hornej/open-task-light/DIYson Express/Printed Parts/STL/Charging Base (optional).stl

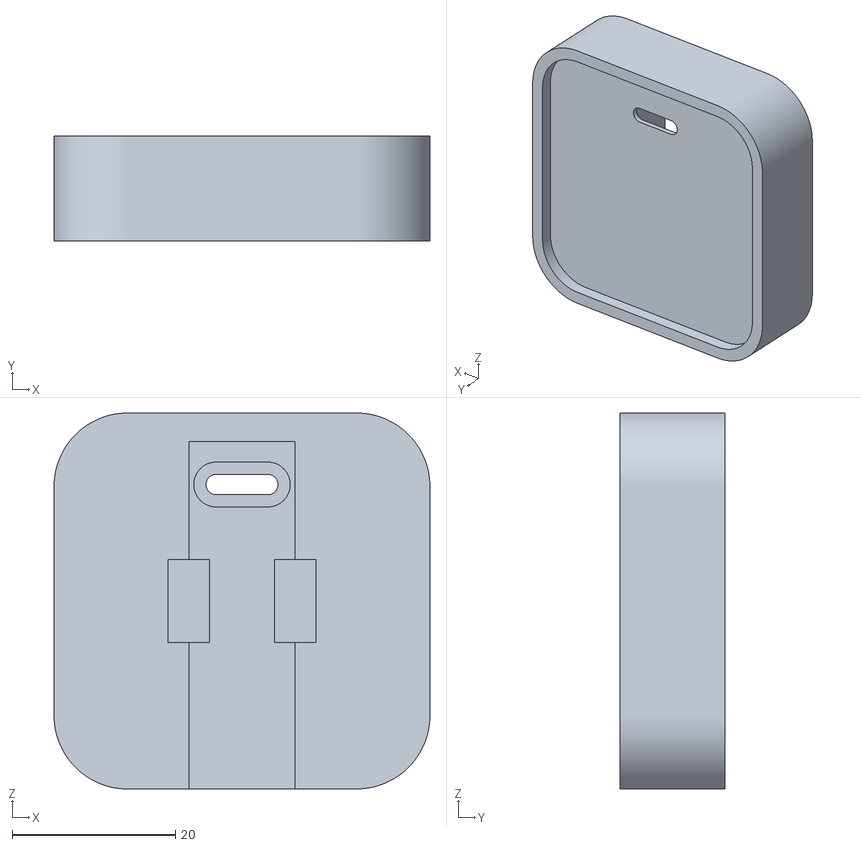
[picture p15: CAD file, 2023-01-30, last stored version]
DIYson Express/Printed Parts/STL/Charging Base (optional).stl
46.0 x 12.8 x 46.0
