hornej/open-task-light/DIYson/Mechanical/STEP/LED Cover - Top.step

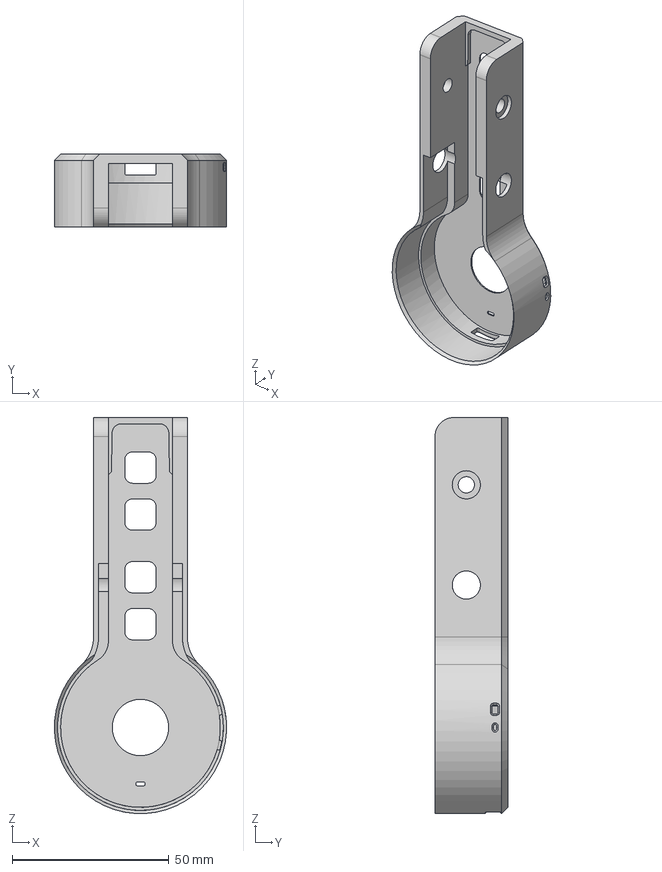
[picture p16: CAD file, 2025-01-30, last stored version]
DIYson/Mechanical/STEP/LED Cover - Top.step
55.0 x 23.3 x 126.5 mm
