hornej/open-task-light/DIYson/Mechanical/STL/Decrease Brightness Button.stl

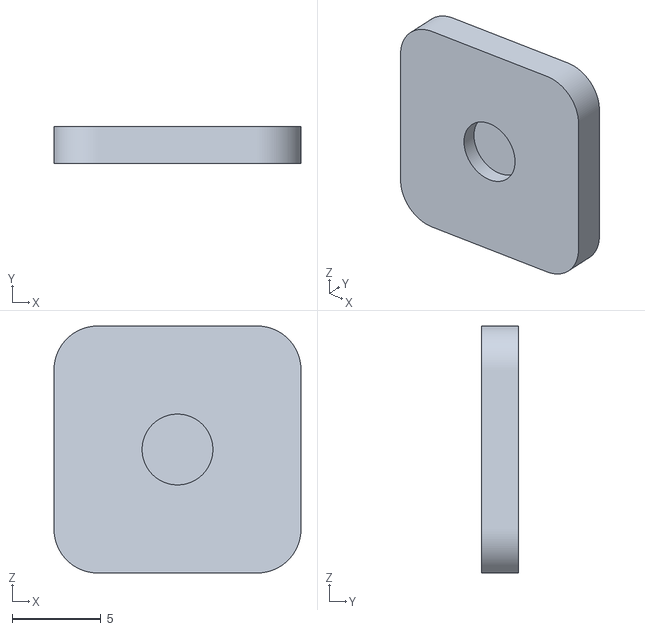
[picture p17: CAD file, 2023-01-05, last stored version]
DIYson/Mechanical/STL/Decrease Brightness Button.stl
13.9 x 2.10 x 14.0
