hornej/open-task-light/DIYson Express/Community-Made Alternatives/jfuchs - Gimbal/Extrusion bracket.stl

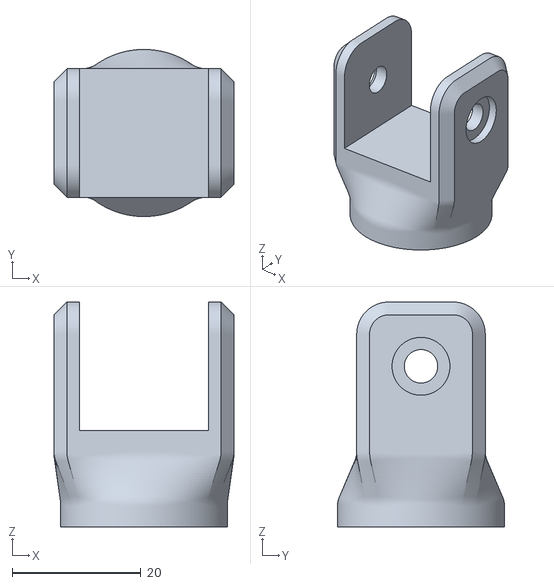
[picture p18: CAD file, 2023-05-03, last stored version]
DIYson Express/Community-Made Alternatives/jfuchs - Gimbal/Extrusion bracket.stl
28.0 x 26.0 x 35.0
