hornej/open-task-light/DIYson Express/Printed Parts/STEP/Pulley Mount.step

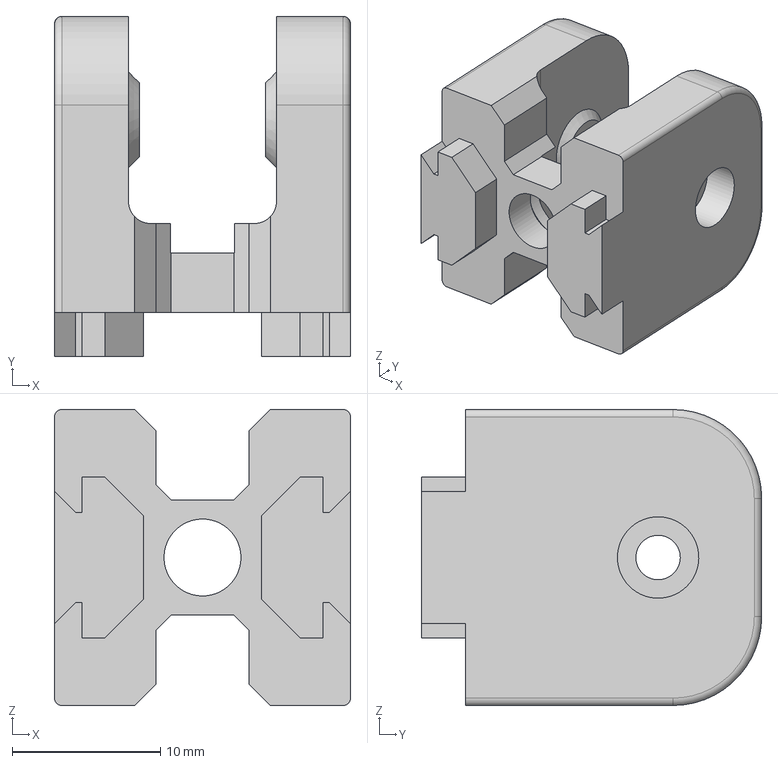
[picture p19: CAD file, 2023-01-31, last stored version]
DIYson Express/Printed Parts/STEP/Pulley Mount.step
20.0 x 23.0 x 20.0 mm
