hornej/open-task-light/DIYson Express/Printed Parts/STL/Counterweight Flex Tab (2x).stl

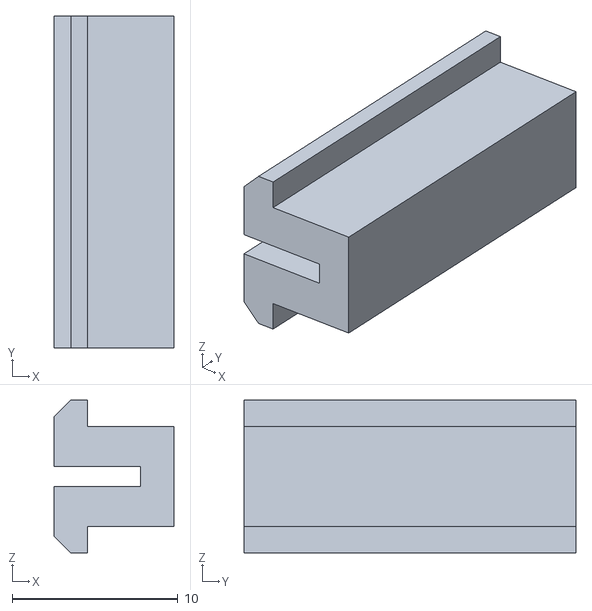
[picture p20: CAD file, 2023-01-30, last stored version]
DIYson Express/Printed Parts/STL/Counterweight Flex Tab (2x).stl
7.20 x 20.0 x 9.20
