hornej/open-task-light/DIYson/Mechanical/STL/Power Button.stl

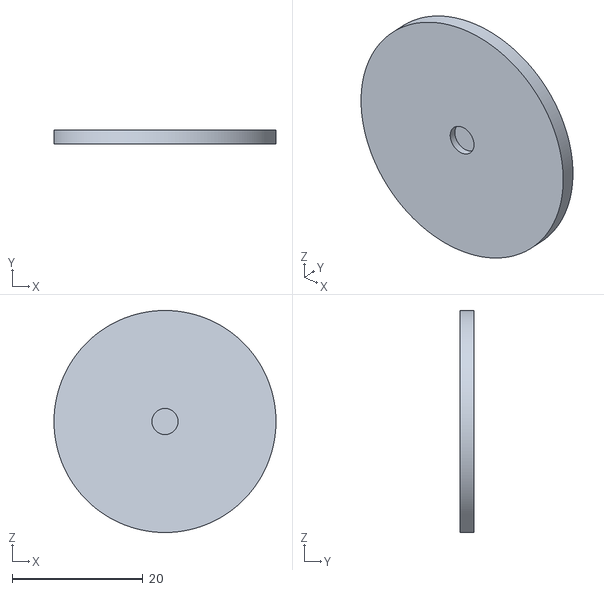
[picture p21: CAD file, 2023-01-05, last stored version]
DIYson/Mechanical/STL/Power Button.stl
33.9 x 2.10 x 33.9
