hornej/open-task-light/DIYson Express/Printed Parts/STEP/Coutnterweight Enclosure.step

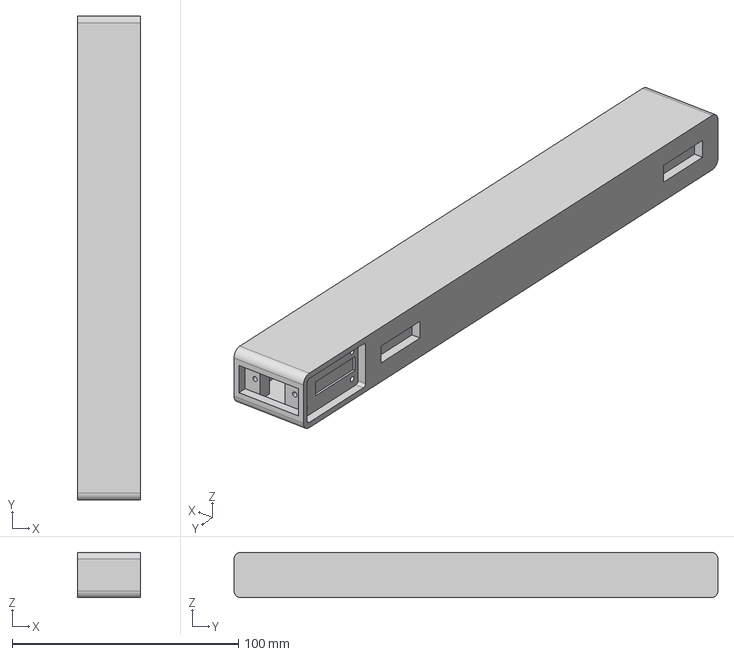
[picture p22: CAD file, 2023-01-31, last stored version]
DIYson Express/Printed Parts/STEP/Coutnterweight Enclosure.step
28.0 x 214.0 x 20.0 mm
