hornej/open-task-light/DIYson/Mechanical/STL/Brightness Button Socket.stl

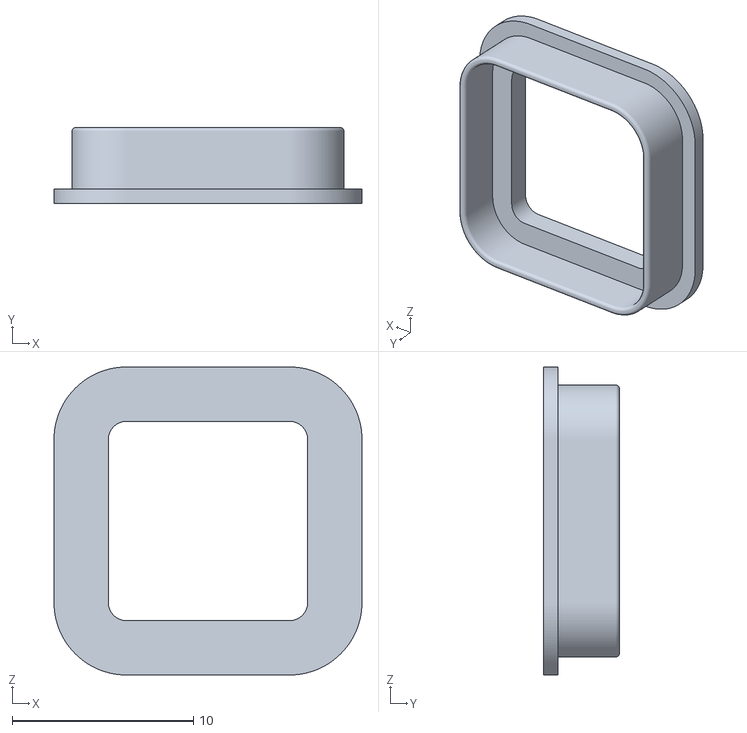
[picture p23: CAD file, 2023-01-05, last stored version]
DIYson/Mechanical/STL/Brightness Button Socket.stl
17.0 x 4.20 x 17.0
