hornej/open-task-light/DIYson/Mechanical/STL/Power Button Socket.stl

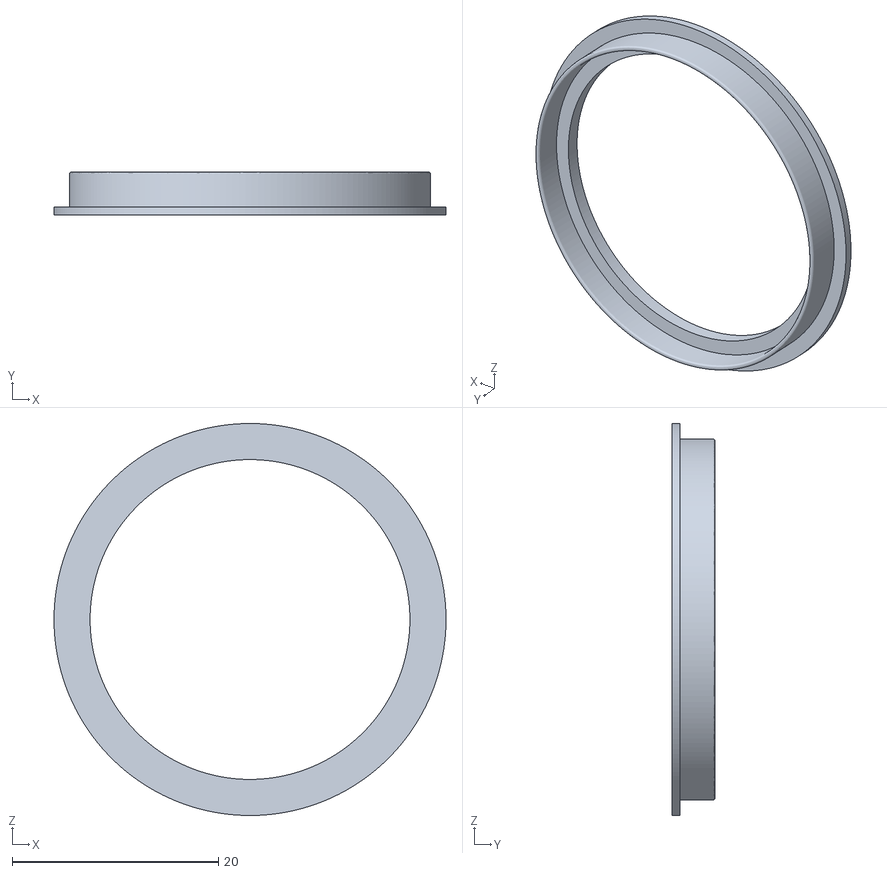
[picture p24: CAD file, 2023-01-05, last stored version]
DIYson/Mechanical/STL/Power Button Socket.stl
38.0 x 4.20 x 38.0
