hornej/open-task-light/DIYson/Printed Parts/STEP/Counterweight.step

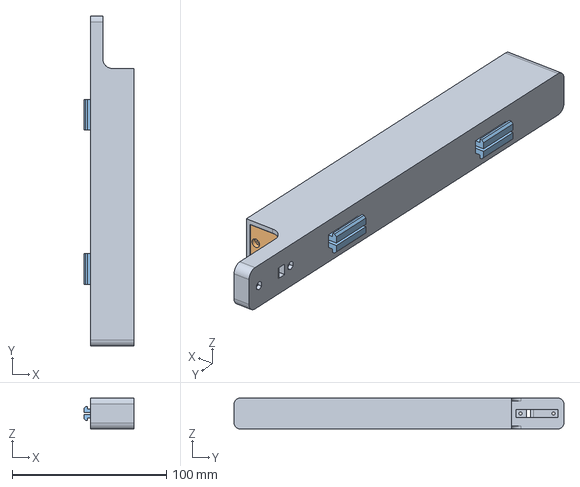
[picture p25: CAD file, 2023-01-30, last stored version]
DIYson/Printed Parts/STEP/Counterweight.step
32.2 x 214.0 x 20.0 mm
Counterweight
Lid
