hornej/open-task-light/DIYson Express/Printed Parts/STEP/Counterweight Belt Clip.step

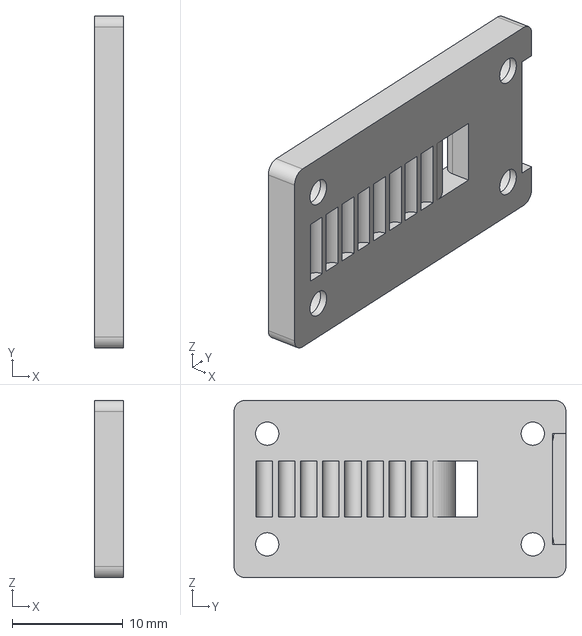
[picture p27: CAD file, 2023-01-31, last stored version]
DIYson Express/Printed Parts/STEP/Counterweight Belt Clip.step
2.60 x 30.0 x 16.0 mm
