hornej/open-task-light/DIYson/Mechanical/STEP/Drag Chain (16 links, print-in-place).stl

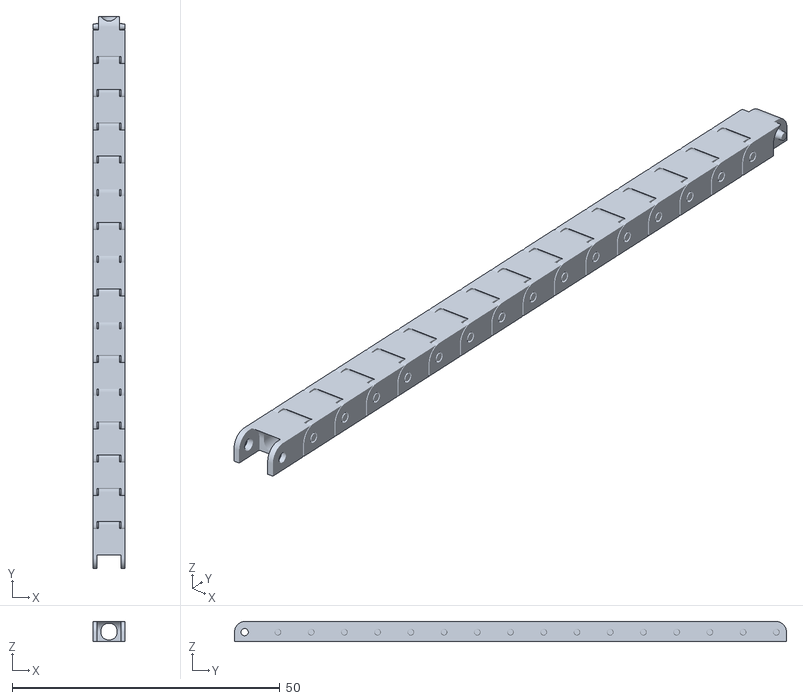
[picture p28: CAD file, 2023-01-05, last stored version]
DIYson/Mechanical/STEP/Drag Chain (16 links, print-in-place).stl
6.00 x 103.0 x 3.75
