hornej/open-task-light/DIYson Express/Printed Parts/STEP/Base.step

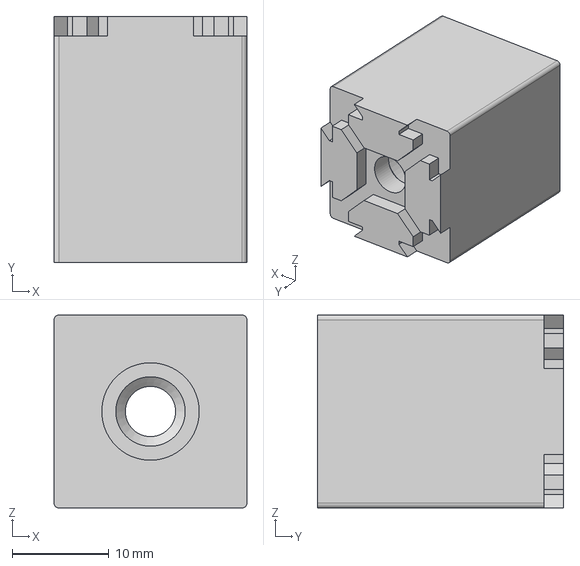
[picture p29: CAD file, 2023-01-31, last stored version]
DIYson Express/Printed Parts/STEP/Base.step
20.0 x 25.5 x 20.0 mm
