hornej/open-task-light/DIYson/Mechanical/STEP/LED Cover Cable Strain Relief Clip.step

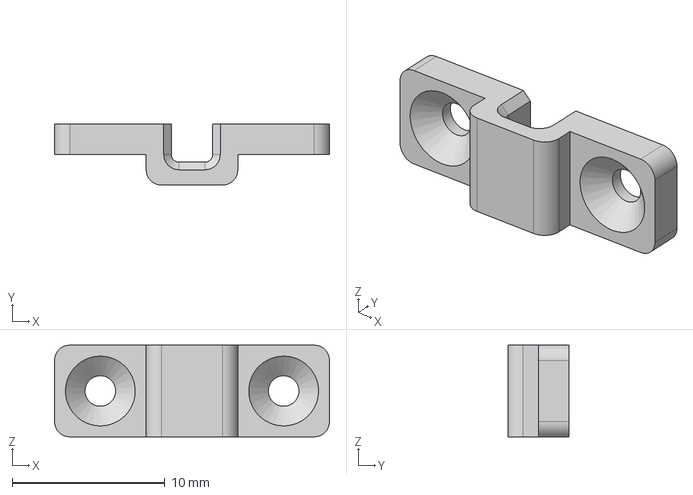
[picture p30: CAD file, 2023-01-05, last stored version]
DIYson/Mechanical/STEP/LED Cover Cable Strain Relief Clip.step
18.0 x 4.00 x 6.00 mm
