hornej/open-task-light/DIYson Express/Printed Parts/STEP/Desk Mount.step

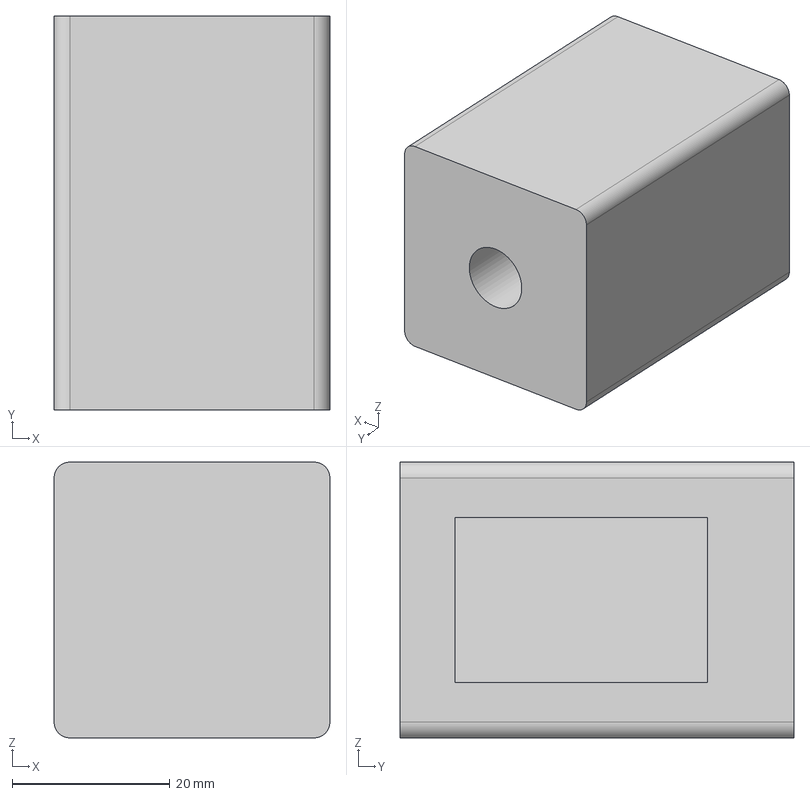
[picture p31: CAD file, 2023-01-31, last stored version]
DIYson Express/Printed Parts/STEP/Desk Mount.step
35.0 x 50.0 x 35.0 mm
