hornej/open-task-light/DIYson/Mechanical/STEP/Button Sockets.step

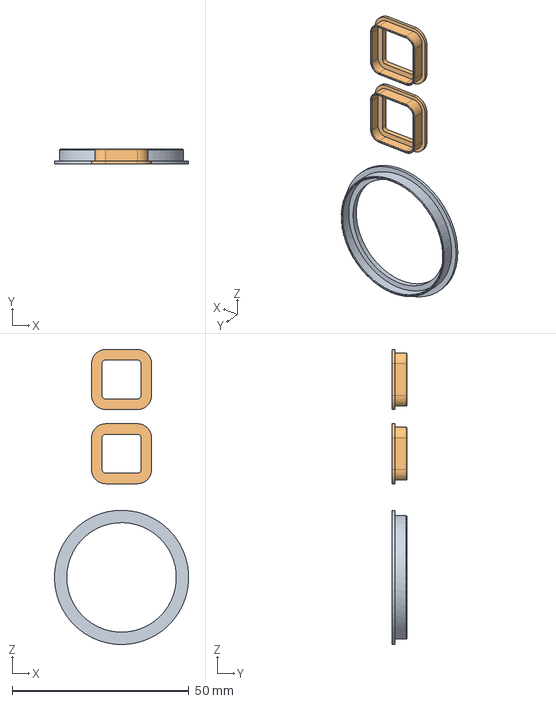
[picture p32: CAD file, 2023-01-05, last stored version]
DIYson/Mechanical/STEP/Button Sockets.step
38.0 x 4.20 x 83.5 mm
