hornej/open-task-light/DIYson/Mechanical/STEP/Buttons.step

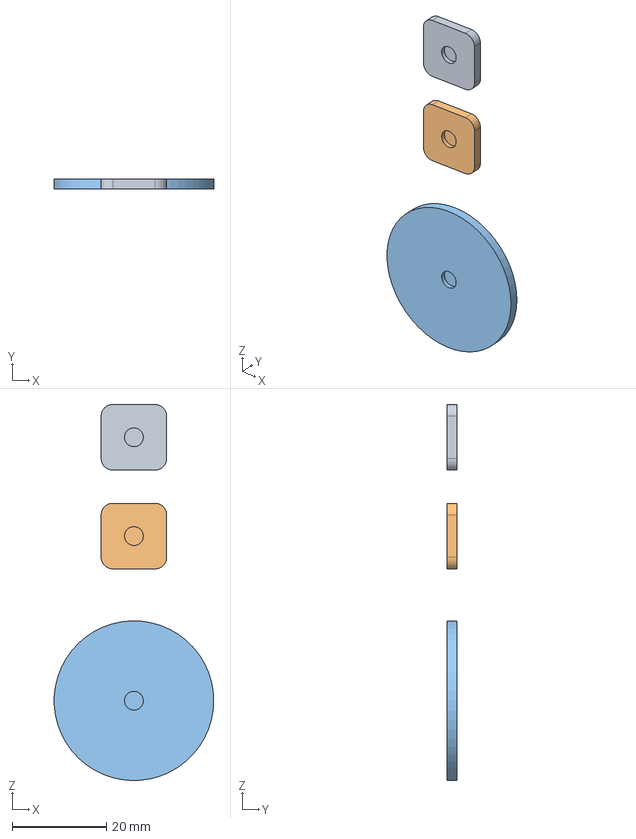
[picture p33: CAD file, 2023-01-05, last stored version]
DIYson/Mechanical/STEP/Buttons.step
33.9 x 2.10 x 79.9 mm
