hornej/open-task-light/DIYson/Mechanical/STEP/Drag Chain Termination (Base).step

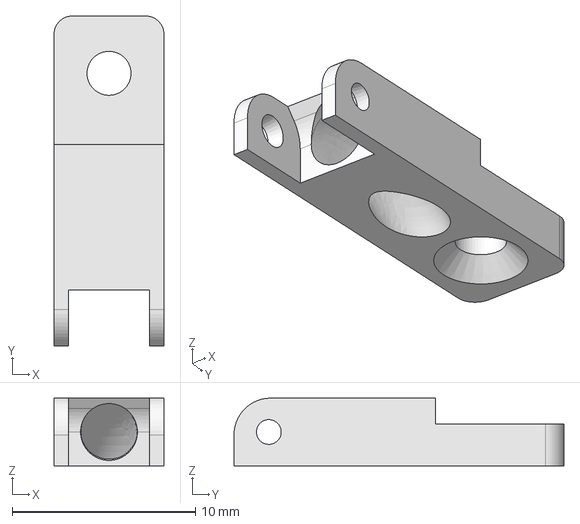
[picture p34: CAD file, 2023-01-05, last stored version]
DIYson/Mechanical/STEP/Drag Chain Termination (Base).step
6.00 x 18.0 x 3.70 mm
