hornej/open-task-light/DIYson/Mechanical/STEP/LED Cover Drag Chain Termination.step

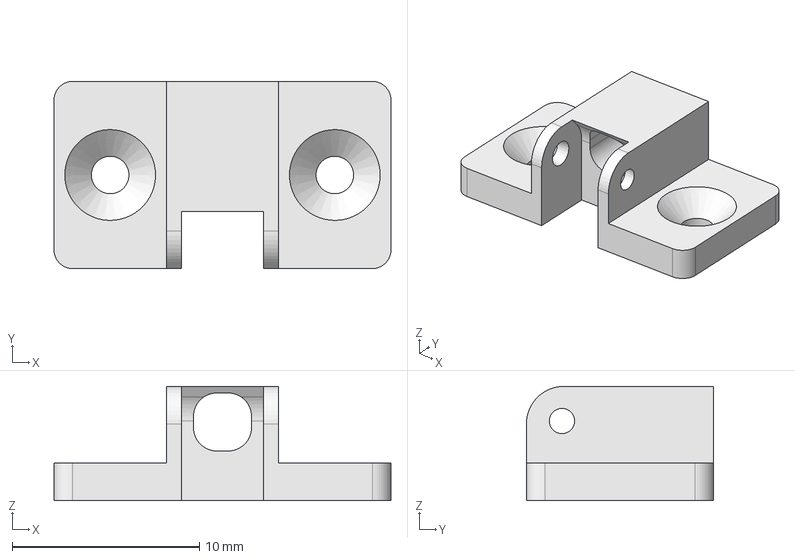
[picture p35: CAD file, 2023-01-05, last stored version]
DIYson/Mechanical/STEP/LED Cover Drag Chain Termination.step
18.0 x 10.0 x 6.10 mm
