hornej/open-task-light/DIYson/Mechanical/STEP/Routed Spacer.step

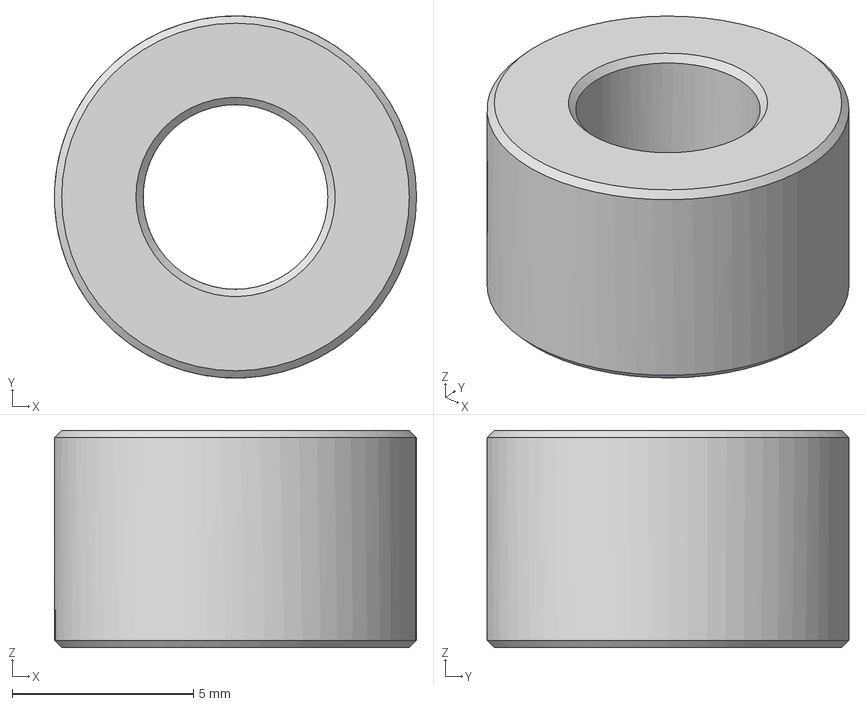
[picture p36: CAD file, 2022-10-18, last stored version]
DIYson/Mechanical/STEP/Routed Spacer.step
10.0 x 10.00 x 6.00 mm
