hornej/open-task-light/DIYson/Mechanical/STEP/Drag Chain Link.step

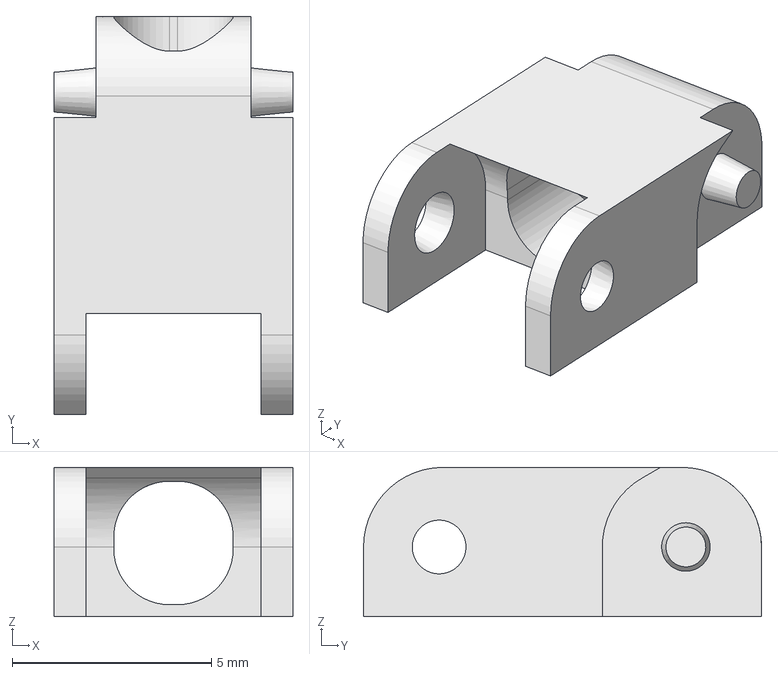
[picture p37: CAD file, 2022-10-18, last stored version]
DIYson/Mechanical/STEP/Drag Chain Link.step
6.00 x 10.0 x 3.75 mm
