hornej/open-task-light/DIYson/Mechanical/STEP/Penultimate Link.step

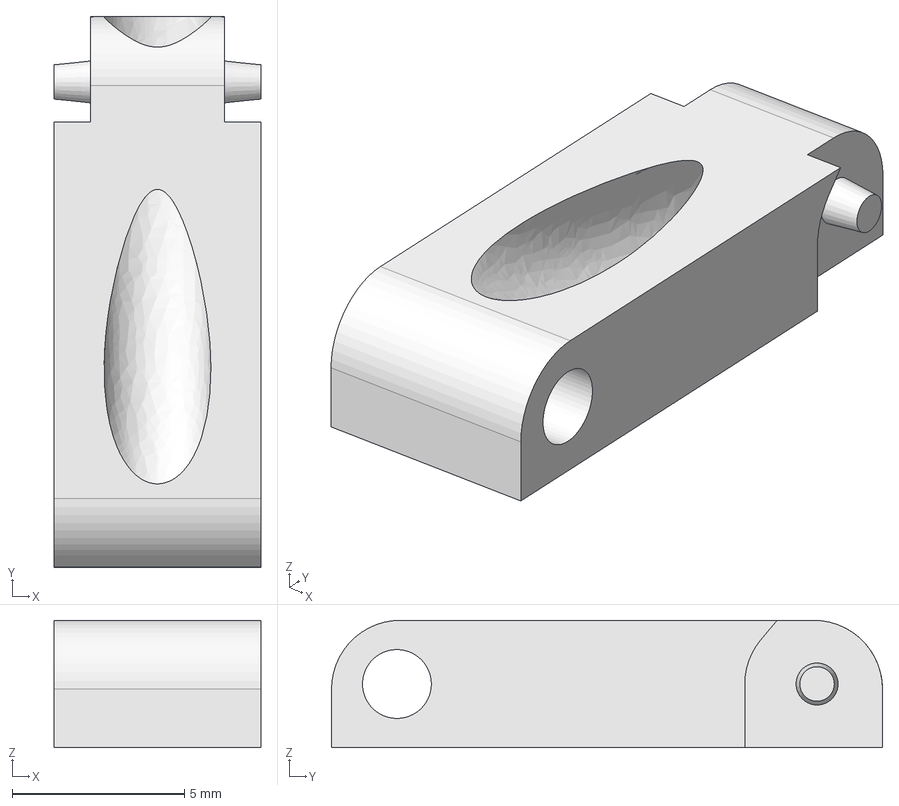
[picture p38: CAD file, 2022-10-18, last stored version]
DIYson/Mechanical/STEP/Penultimate Link.step
6.00 x 16.0 x 3.70 mm
