hornej/open-task-light/DIYson/Mechanical/STEP/Drag Chain Carriage Clip.step

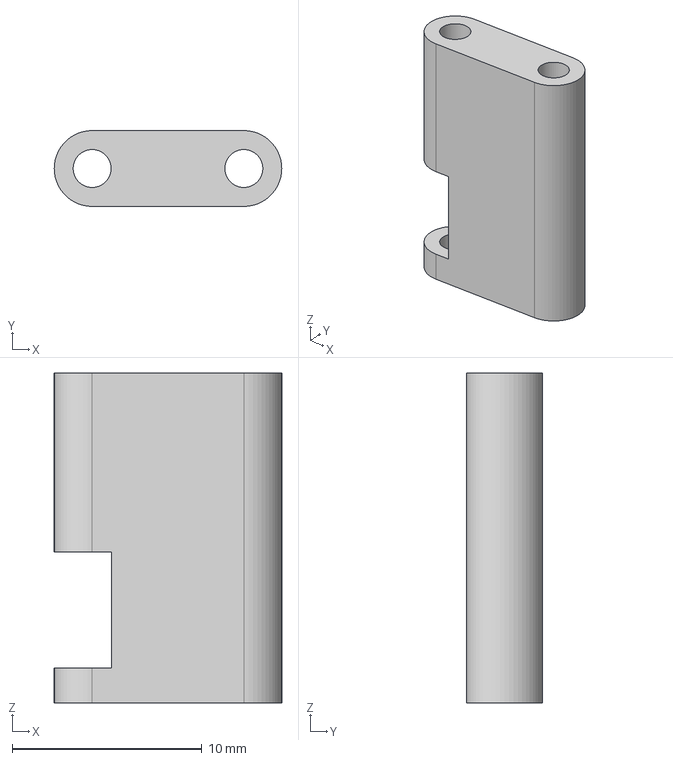
[picture p39: CAD file, 2022-10-18, last stored version]
DIYson/Mechanical/STEP/Drag Chain Carriage Clip.step
12.0 x 4.00 x 17.4 mm
